Agent-Bid/OpenWave/Firmware/OpenWave_Firmware/src/symbols.h

#include <Arduino.h>
#include <Adafruit_SSD1306.h>
//Custom Symbol Library for the Walkman

//Battery Symbol
const unsigned char battery[] PROGMEM = {
  0xff,
  0xfc,
  0xff,
  0xff,
  0xff,
  0xff,
  0xff,
  0xfc,
  0xff,
  0xfc,
  0xff,
  0xff,
  0xff,
  0xff,
  0xff,
  0xfc
};

//Music Symbol 1 Part 1
const unsigned char musicnote1[] PROGMEM = {
  0x00,
  0x00,
  0x00,
  0x00,
  0x00,
  0x01,
  0x80,
  0x00,
  0x00,
  0x01,
  0xc0,
  0x00,
  0x00,
  0x01,
  0xf0,
  0x00,
  0x00,
  0x01,
  0xf8,
  0x00,
  0x00,
  0x01,
  0xfe,
  0x00,
  0x00,
  0x01,
  0xff,
  0x00,
  0x00,
  0x01,
  0xff,
  0x80,
  0x00,
  0x01,
  0xff,
  0x80,
  0x00,
  0x01,
  0xe3,
  0xc0,
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
};

//Music Symbol 1 Part 2 
const unsigned char musicnote2[] PROGMEM = {
  0x00,
  0x00,
  0x00,
  0x00,
  0x00,
  0x00,
  0x00,
  0x00,
  0x00,
  0x00,
  0x00,
  0x00,
  0x00,
  0x00,
  0x00,
  0x00,
  0x00,
  0x00,
  0x00,
  0x00,
  0x00,
  0x00,
  0x00,
  0x00,
  0x00,
  0x00,
  0x00,
  0x00,
  0x00,
  0x00,
  0x1c,
  0x00,
  0x00,
  0x01,
  0xfc,
  0x00,
  0x00,
  0x0f,
  0xfc,
  0x00,
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
};
